shiebin-bit/smart-room-safety-comfort/screenshots/dashboard-cardfix-confirm.png

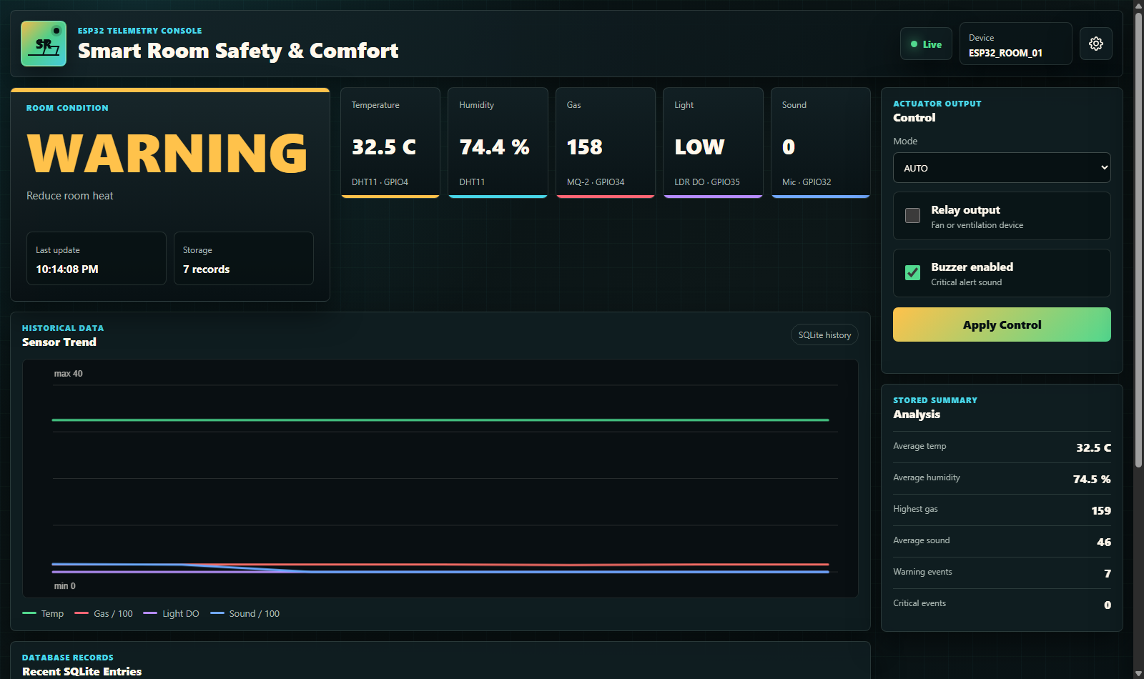
screenshots/dashboard-cardfix-confirm.png
