shiebin-bit/smart-room-safety-comfort/screenshots/dashboard-four-trends-final.png

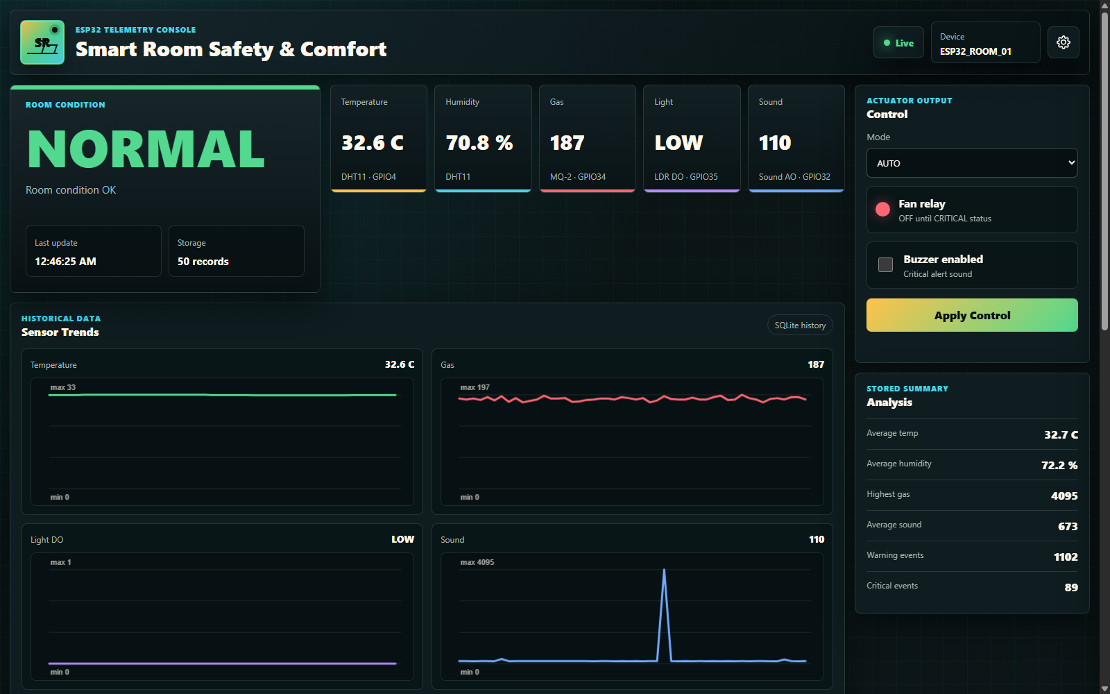
screenshots/dashboard-four-trends-final.png
