shiebin-bit/smart-room-safety-comfort/screenshots/dashboard/dashboard-desktop2.png

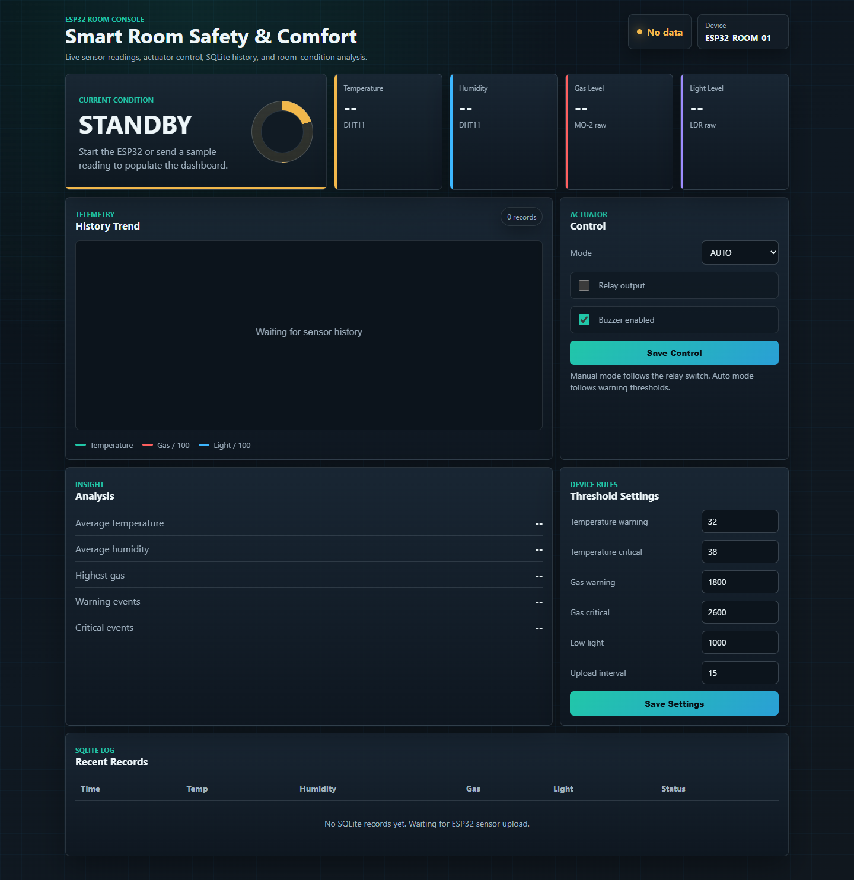
screenshots/dashboard/dashboard-desktop2.png
