shiebin-bit/smart-room-safety-comfort/screenshots/dashboard/dashboard-mobile-full.png

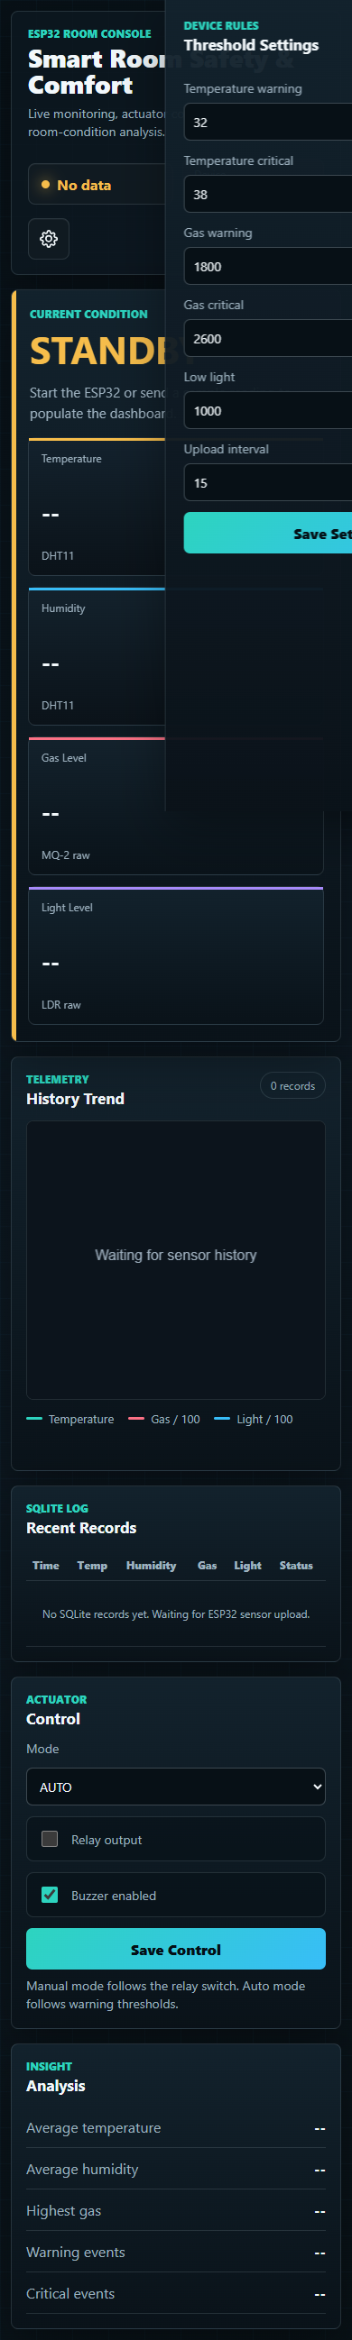
screenshots/dashboard/dashboard-mobile-full.png
